MATTMCCA/PWM-FAN/pics/001.png

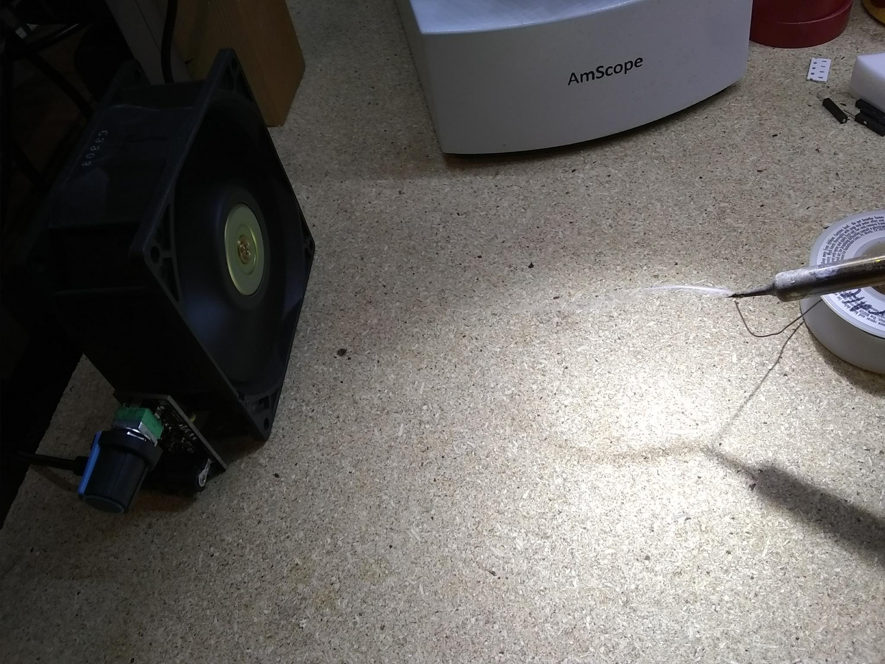
pics/001.png
