MATTMCCA/PWM-FAN/pics/004.png

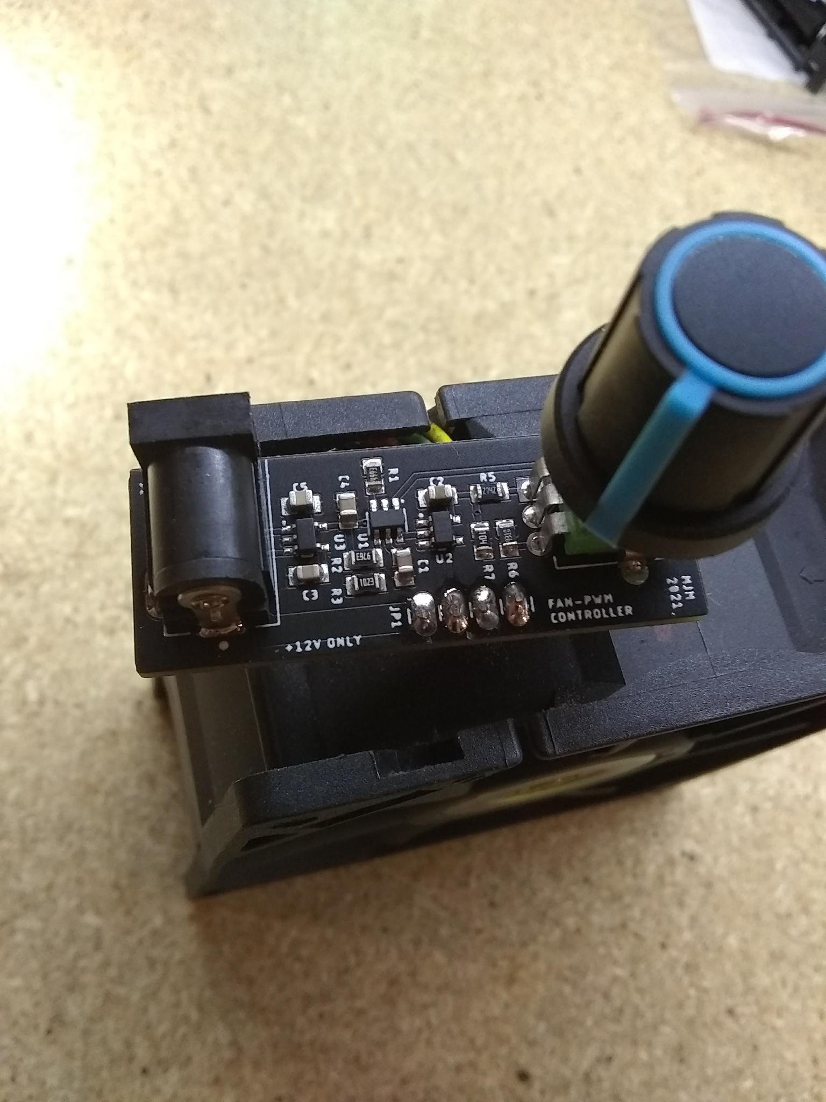
pics/004.png
