MATTMCCA/PWM-FAN/pics/005.png

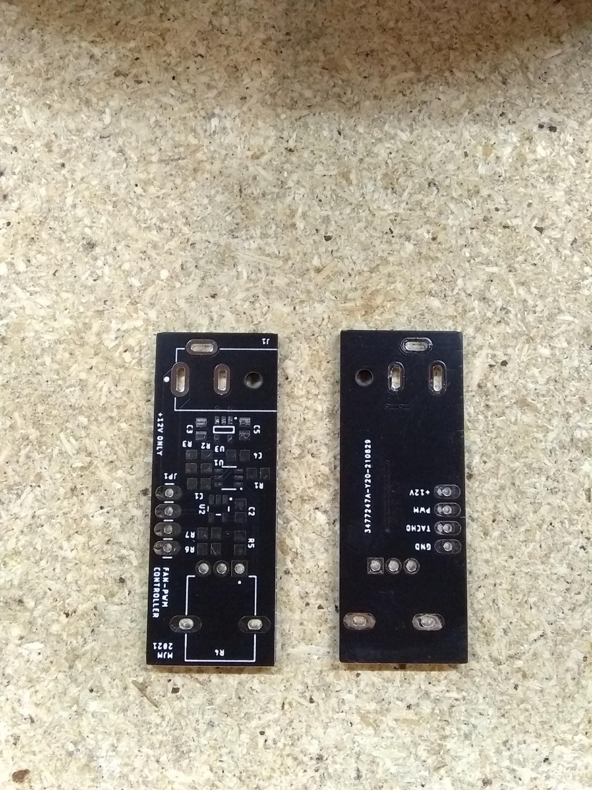
pics/005.png
